BryceBeagle/idiotic/eagle/modules/door-sensor/board.png

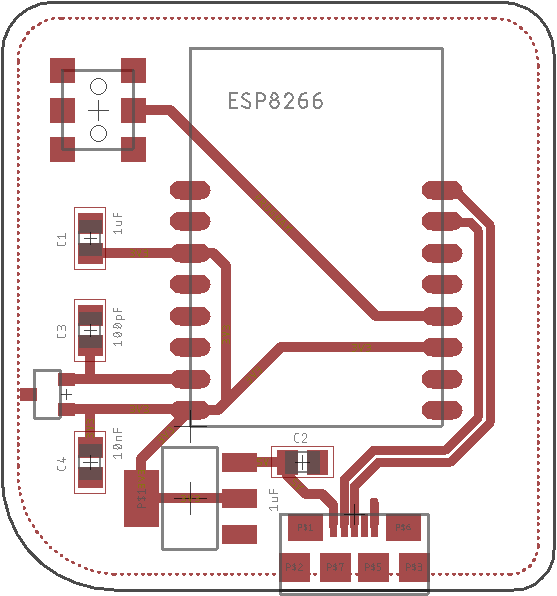
eagle/modules/door-sensor/board.png
