BryceBeagle/idiotic/eagle/modules/door-sensor/shematic.png

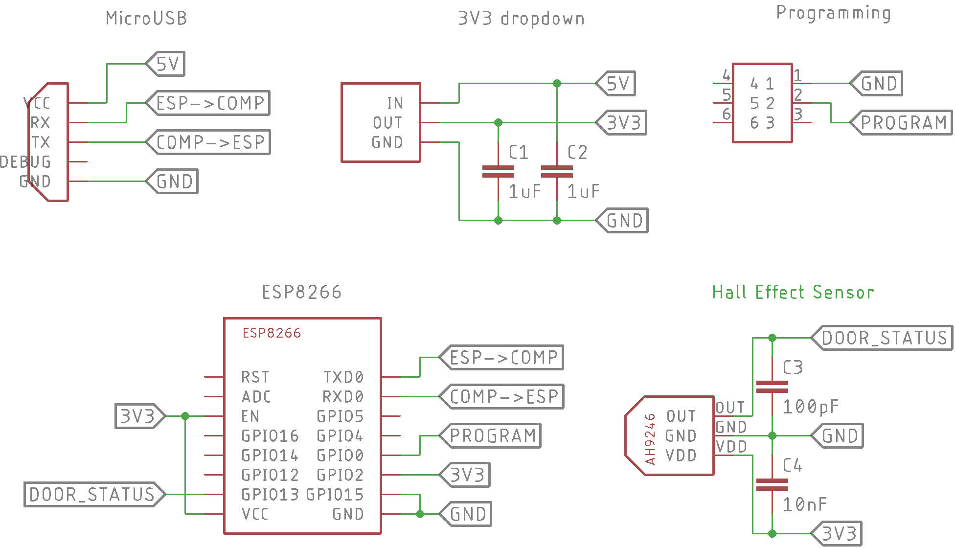
eagle/modules/door-sensor/shematic.png
