BryceBeagle/idiotic/eagle/modules/ir/board.png

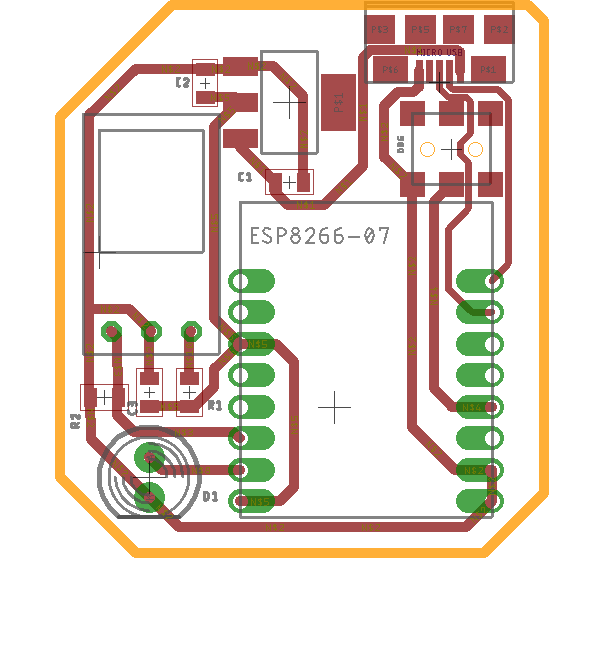
eagle/modules/ir/board.png
