BryceBeagle/idiotic/eagle/modules/temp-sensor/board.png

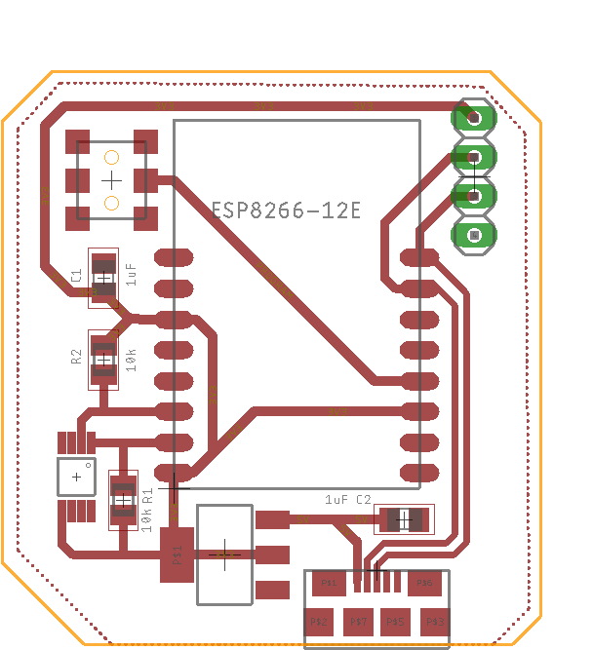
eagle/modules/temp-sensor/board.png
